zoroseerus/g305lithiummodkit/pics/IMG_1834.JPEG

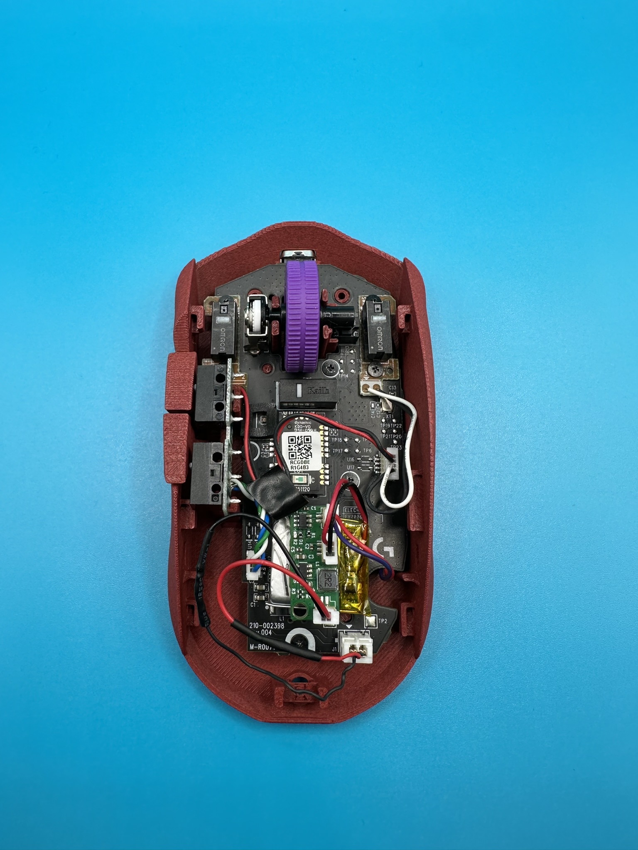
pics/IMG_1834.JPEG
