zoroseerus/g305lithiummodkit/pics/IMG_1837.JPEG

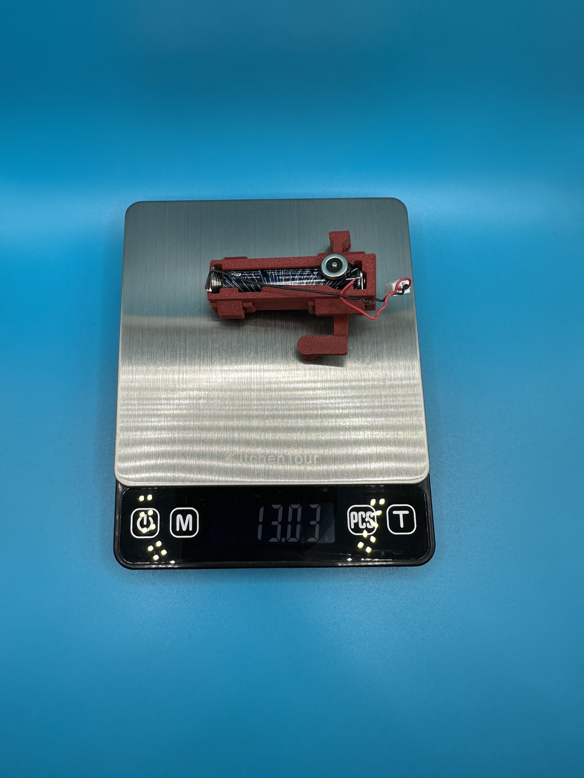
pics/IMG_1837.JPEG
