zoroseerus/g305lithiummodkit/pics/IMG_1838.JPEG

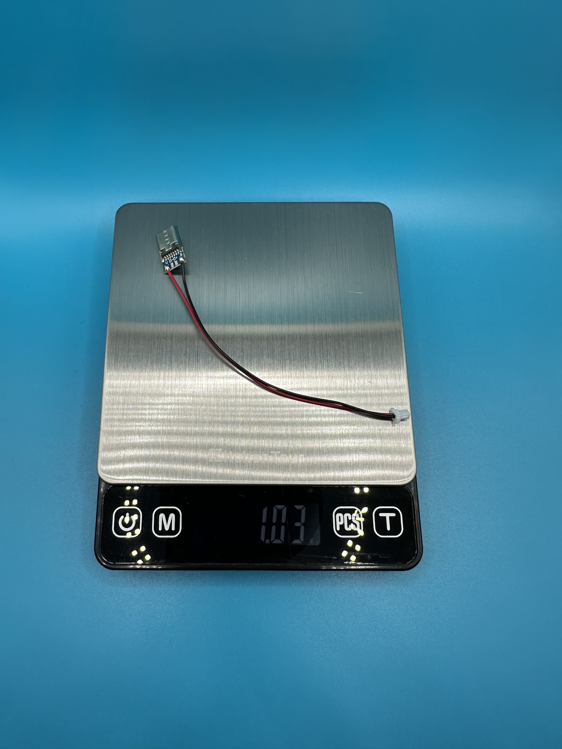
pics/IMG_1838.JPEG
