zoroseerus/g305lithiummodkit/pics/IMG_1839.JPEG

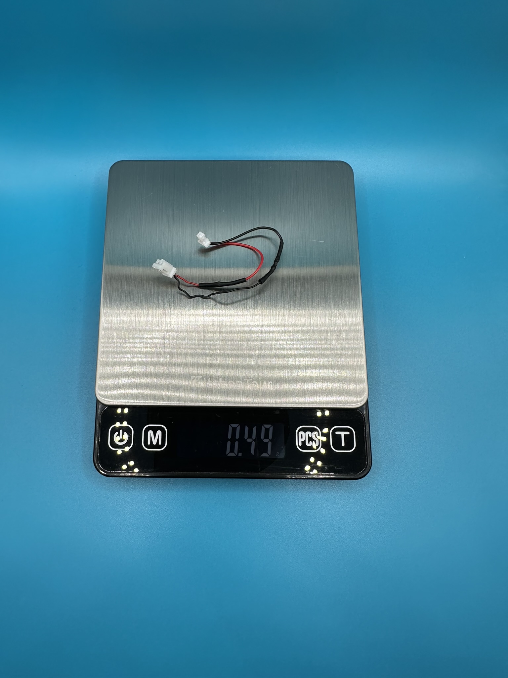
pics/IMG_1839.JPEG
