zoroseerus/g305lithiummodkit/pics/IMG_1841.JPEG

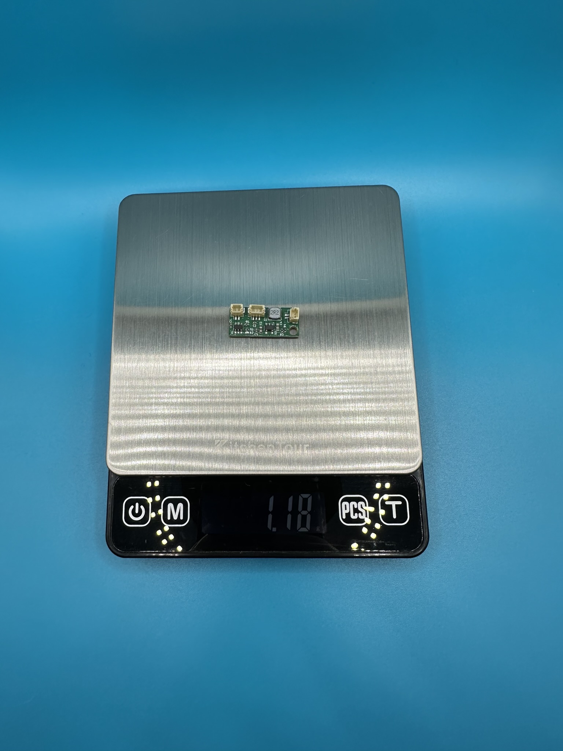
pics/IMG_1841.JPEG
