zoroseerus/g305lithiummodkit/pics/IMG_1842.JPEG

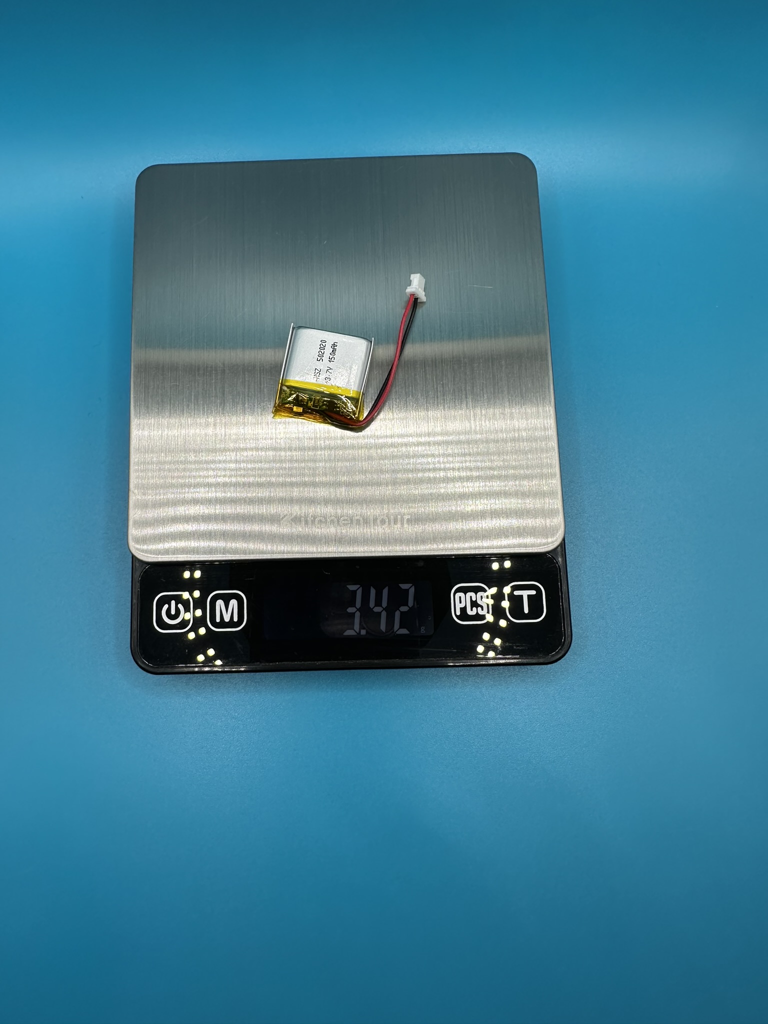
pics/IMG_1842.JPEG
