zoroseerus/g305lithiummodkit/JLPCB Ordering Guide/image (1).png

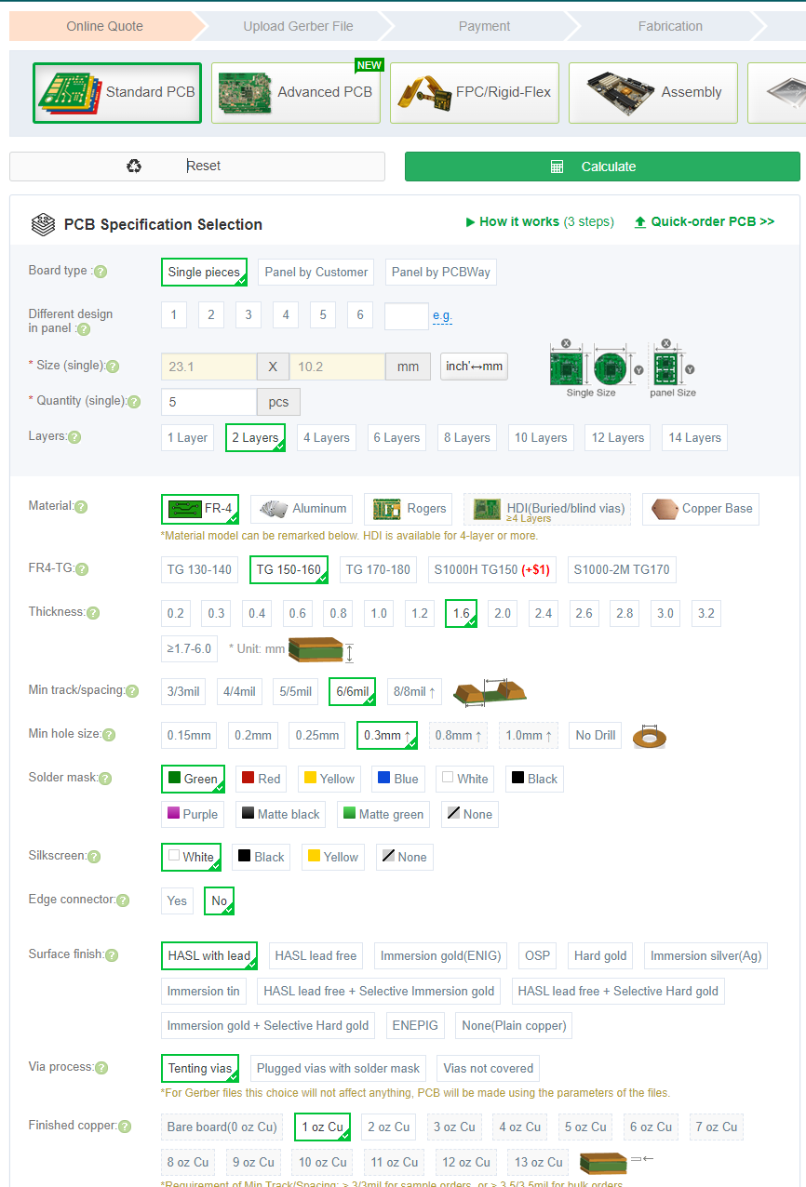
JLPCB Ordering Guide/image (1).png
