zoroseerus/g305lithiummodkit/JLPCB Ordering Guide/image (4).png

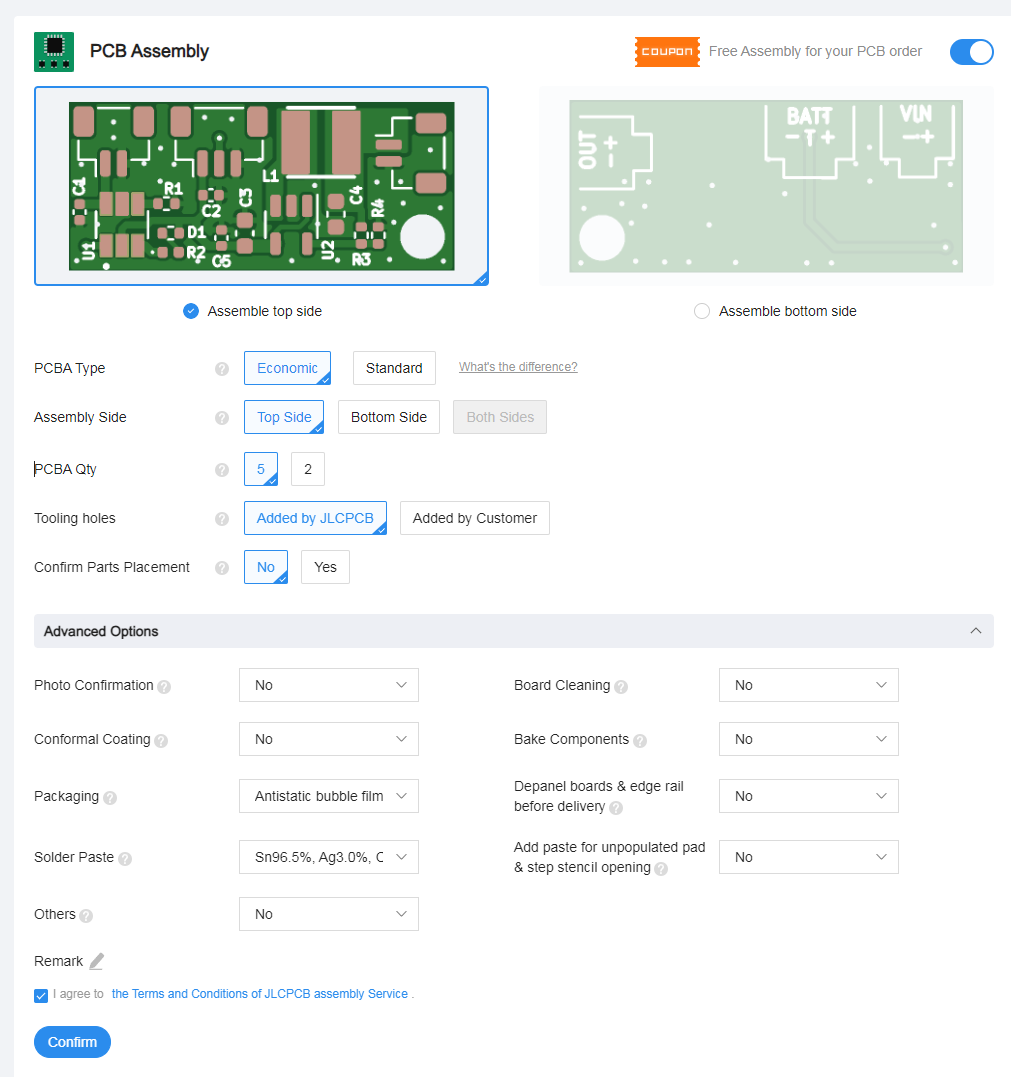
JLPCB Ordering Guide/image (4).png
