zoroseerus/g305lithiummodkit/JLPCB Ordering Guide/image (5-2).png

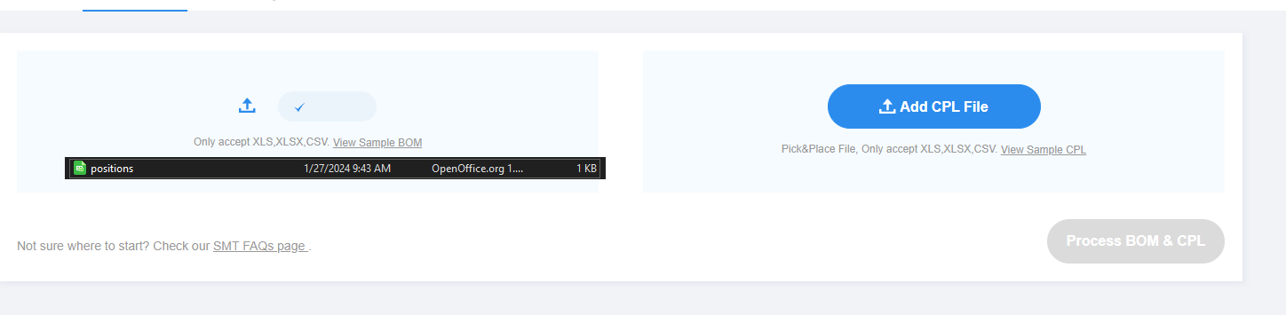
JLPCB Ordering Guide/image (5-2).png
