zoroseerus/g305lithiummodkit/JLPCB Ordering Guide/image (6).png

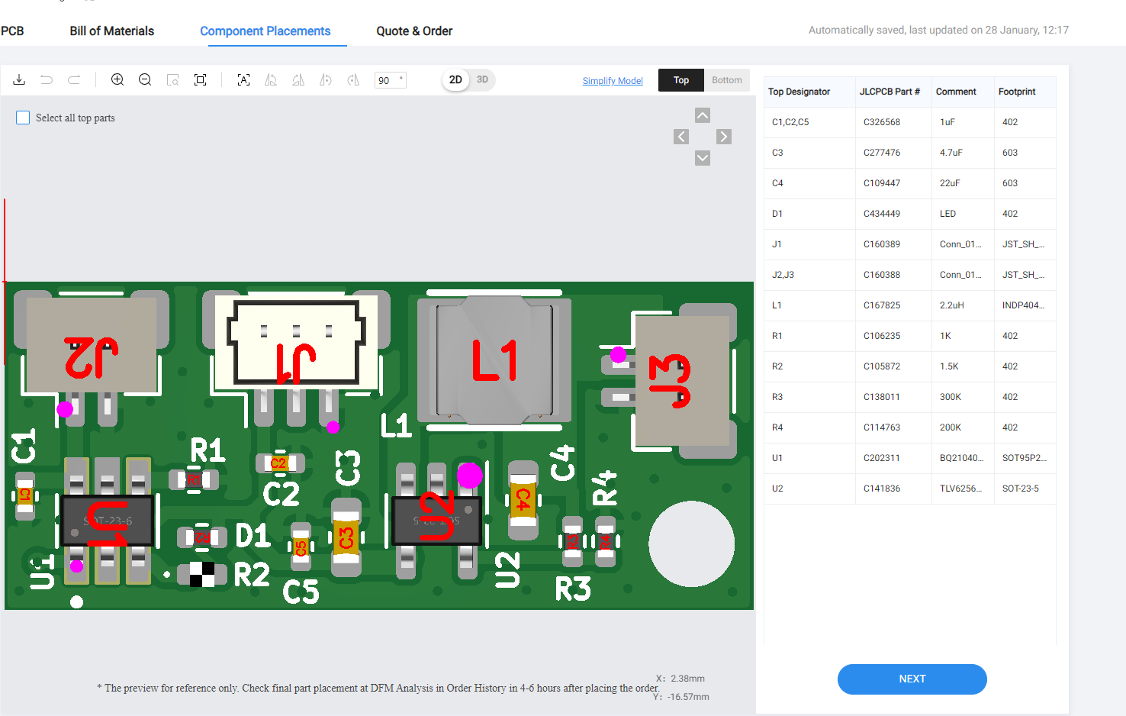
JLPCB Ordering Guide/image (6).png
